ehaag/TBP_Lighting/img/Acc_DCLabel.jpg

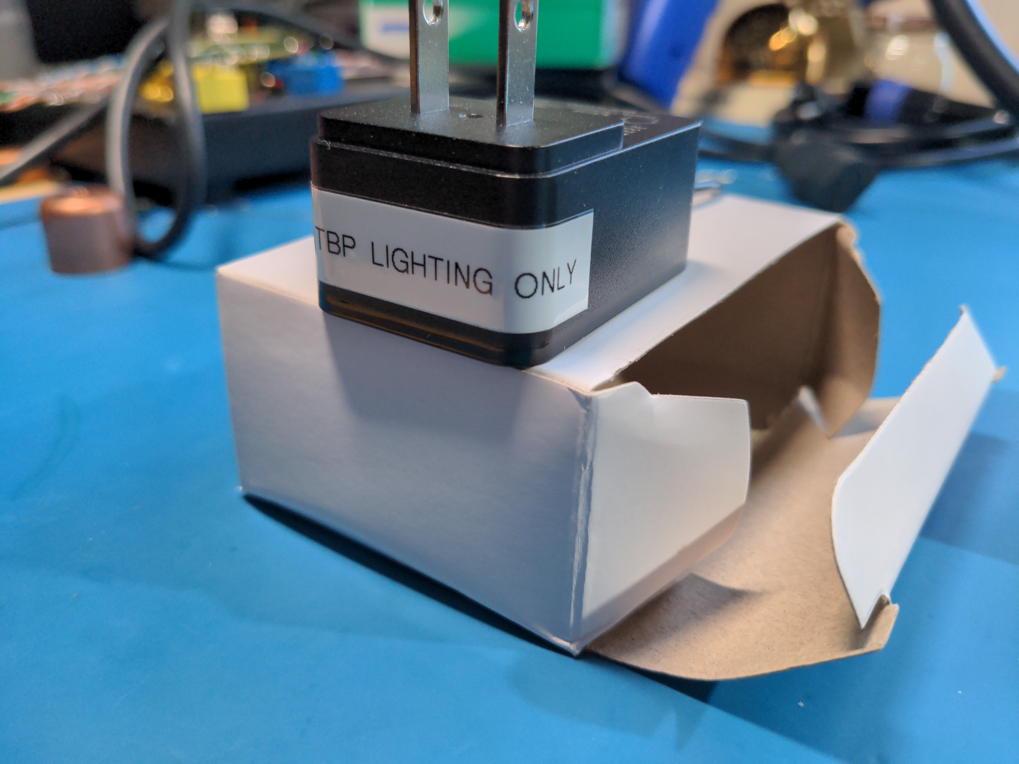
img/Acc_DCLabel.jpg
