ehaag/TBP_Lighting/img/Acc_DCMarkings.jpg

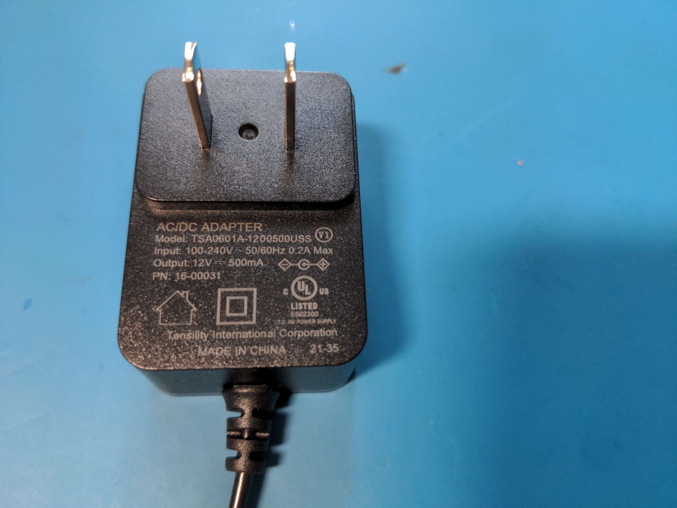
img/Acc_DCMarkings.jpg
