ehaag/TBP_Lighting/img/Ctrl_DCin.jpg

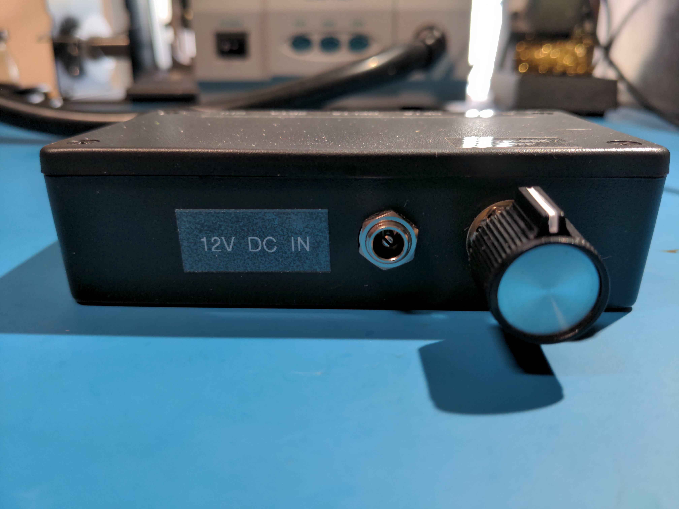
img/Ctrl_DCin.jpg
