ehaag/TBP_Lighting/img/Ctrl_Jacks3q.jpg

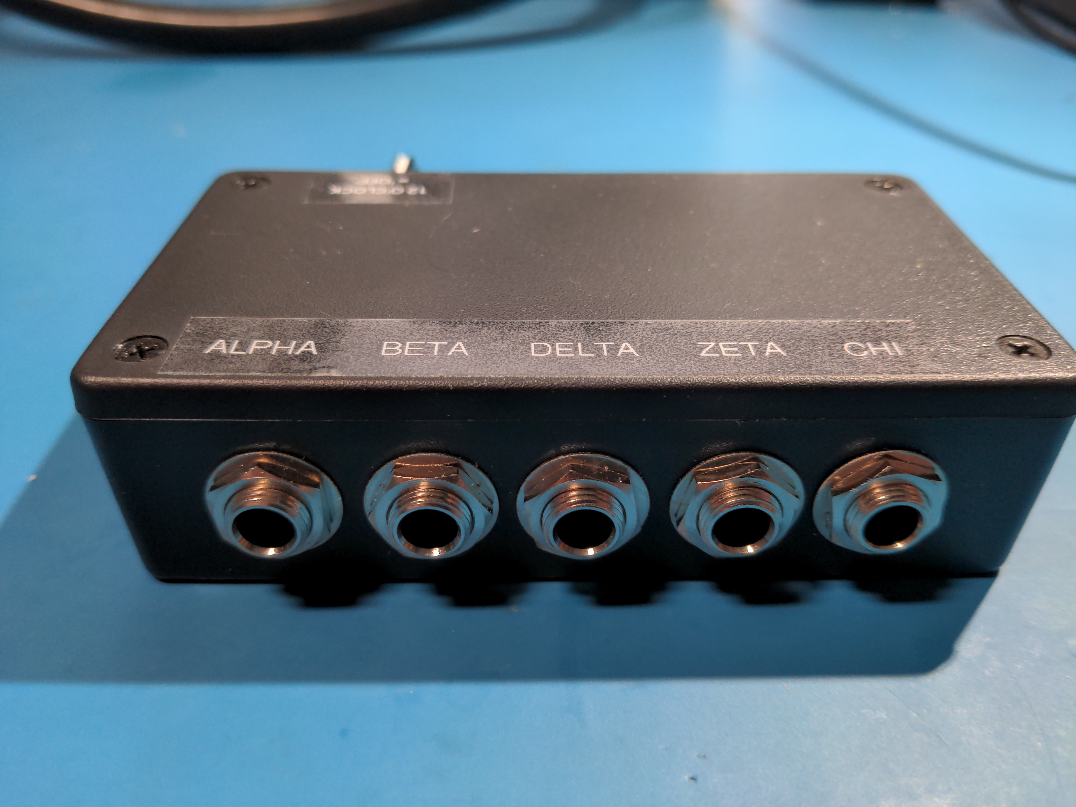
img/Ctrl_Jacks3q.jpg
