ehaag/TBP_Lighting/img/Ctrl_Knob3q.jpg

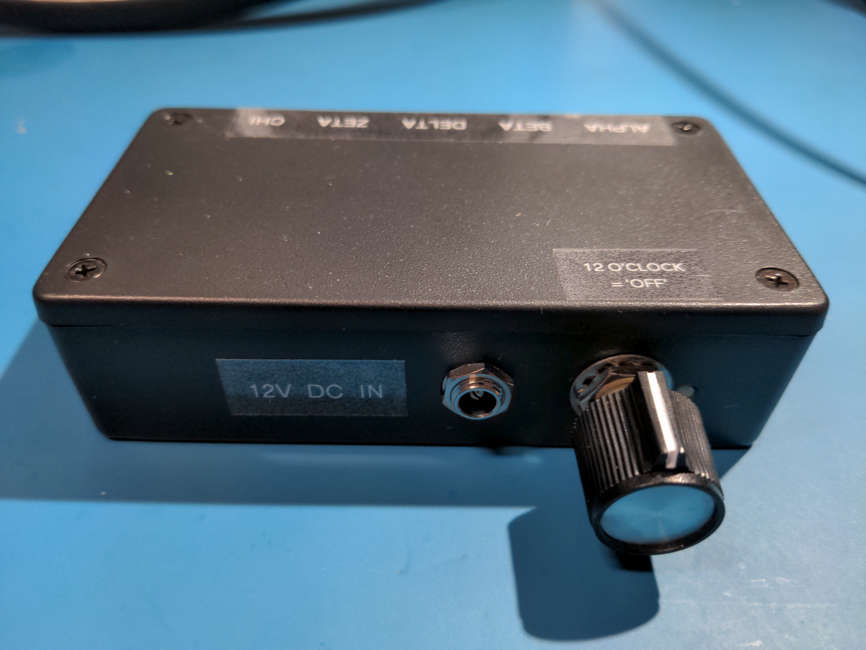
img/Ctrl_Knob3q.jpg
