ehaag/TBP_Lighting/img/Lamp_Side.jpg

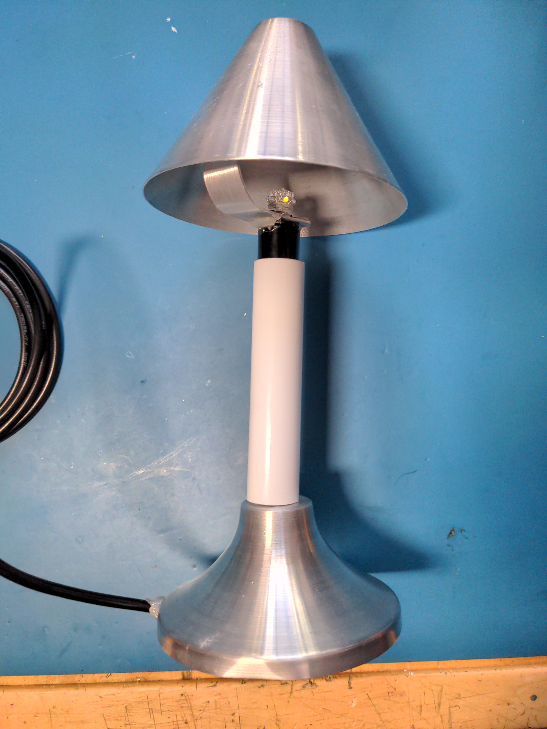
img/Lamp_Side.jpg
