ehaag/TBP_Lighting/img/Seq_Posn0AB.jpg

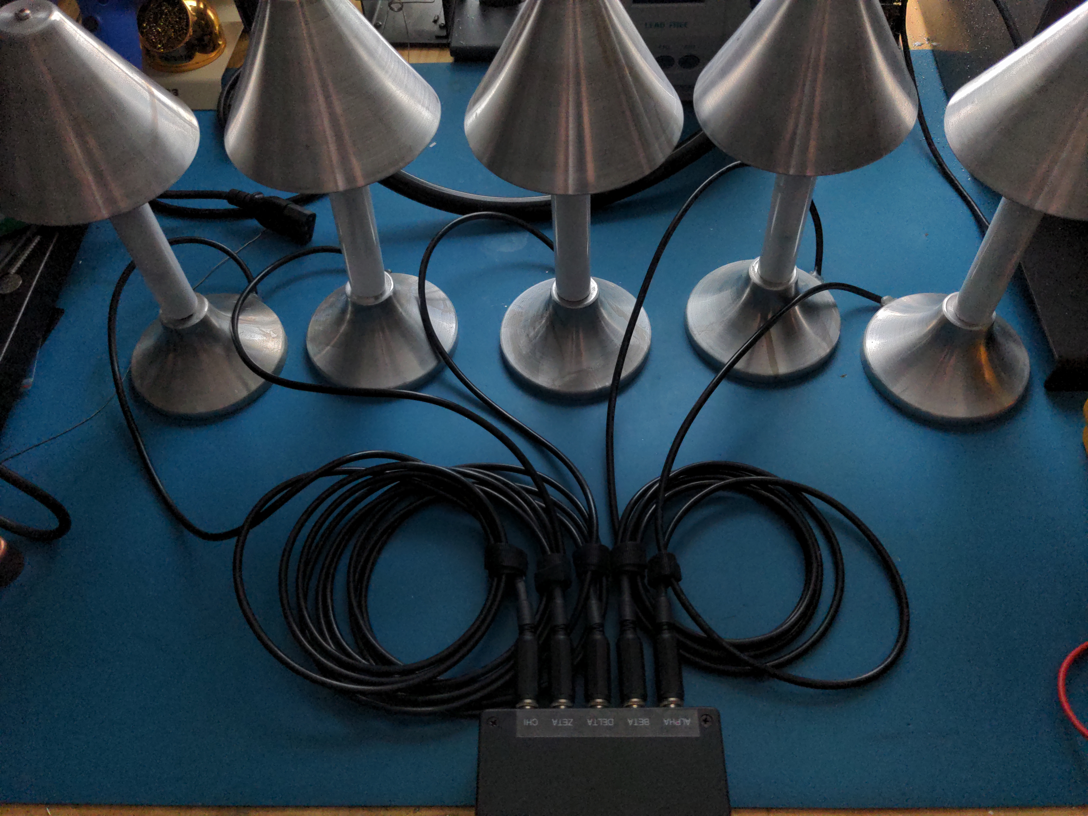
img/Seq_Posn0AB.jpg
