ehaag/TBP_Lighting/img/Seq_Posn2.jpg

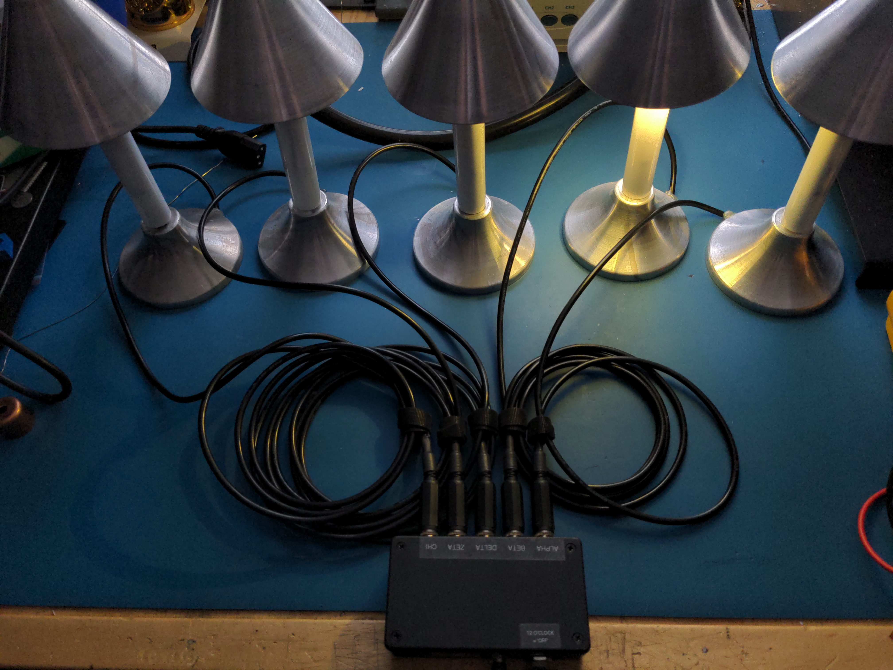
img/Seq_Posn2.jpg
