ehaag/TBP_Lighting/img/Seq_Posn8.jpg

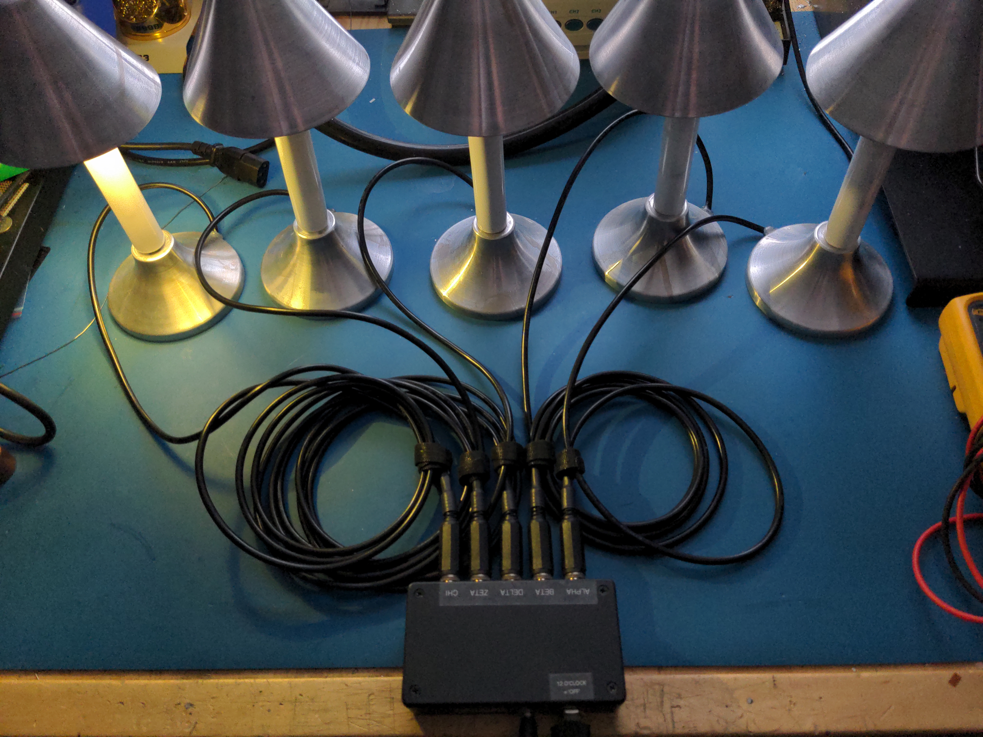
img/Seq_Posn8.jpg
