ehaag/TBP_Lighting/img/Seq_Posn13579.jpg

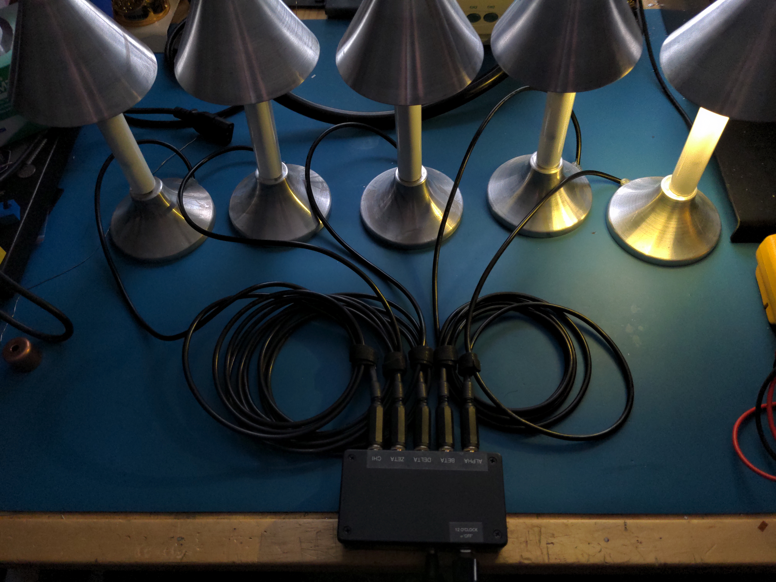
img/Seq_Posn13579.jpg
