ehaag/TBP_Lighting/pcb/LTSpice/TBP_Protection_Sim.asc

C3: polcap; 10µ; V=25 Irms=1.12694 Rser=0.1 Lser=0 mfg="KEMET" pn="T521B106M025ATE100" type="Tantalum"
D1: zener; UDZV16B
M1: pmos; Si2369DS
M2: pmos; Si2369DS
M3: nmos; AO3404A
R1: res; 100k
R2: res; 390
R3: res; 1.5
R4: res; 10k
R5: res; 33k
R6: res; 6k8
R7: res; 47k
R8: res; 27k
R9: res; 10k
R10: res; 330k
U1: ATL431A_TRANS
V1: voltage; PULSE(16 -16 0 2 2 1m 4.001)
Named nets: 0, TP1, TP2, TP3, TP4, TP5, TP6, TP7, TP8, TP9
.dc V1 -20 20 10m
.lib "Si2369DS_PS.LIB"
.lib "AO3404.mod"
.lib "ATL431A_TRANS.LIB"
